martinberlin/H-spi-adapters/1.54-sharp-lcd/schematic/sharp-lcd-back.png

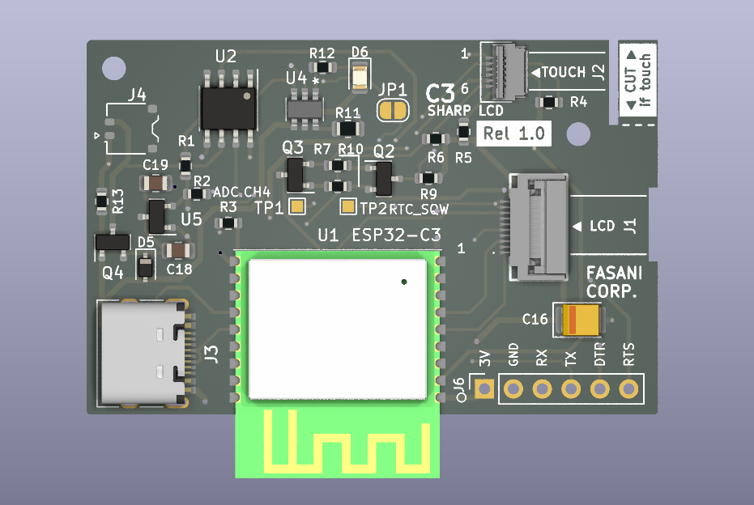
1.54-sharp-lcd/schematic/sharp-lcd-back.png
