martinberlin/H-spi-adapters/1.54-watch-pcb/schematic/EPD_drawing/gooddisplay-GDEY0154D67.jpg

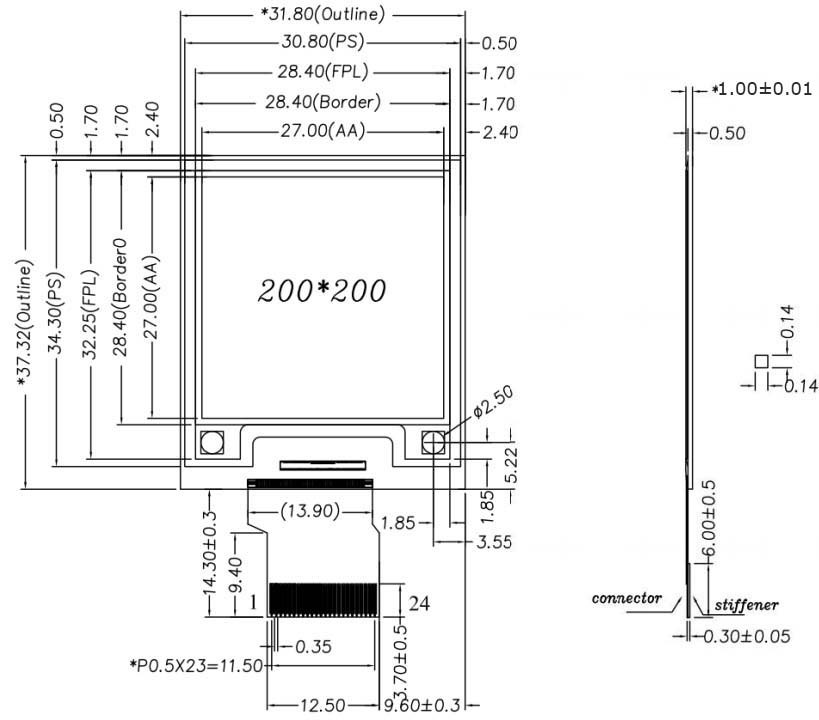
1.54-watch-pcb/schematic/EPD_drawing/gooddisplay-GDEY0154D67.jpg
