martinberlin/H-spi-adapters/tinypico-uc8156/parts/3d/MOSFET_8EDL-T1-GE3_VIS.step

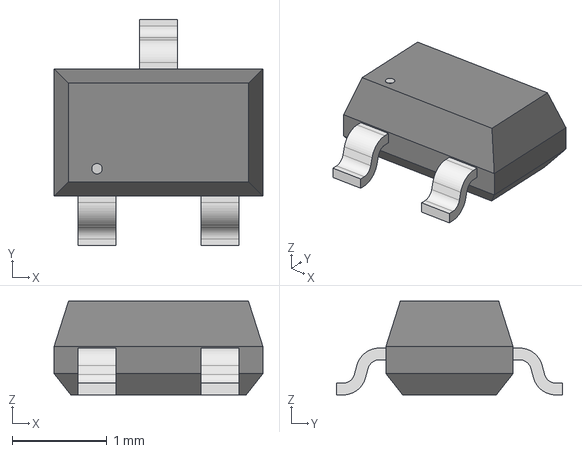
[picture p32: CAD file, 2022-03-19]
tinypico-uc8156/parts/3d/MOSFET_8EDL-T1-GE3_VIS.step
2.21 x 2.39 x 0.993 mm
