martinberlin/H-spi-adapters/sharp-lcd-27/parts/3d/Button_SKRKAH.step

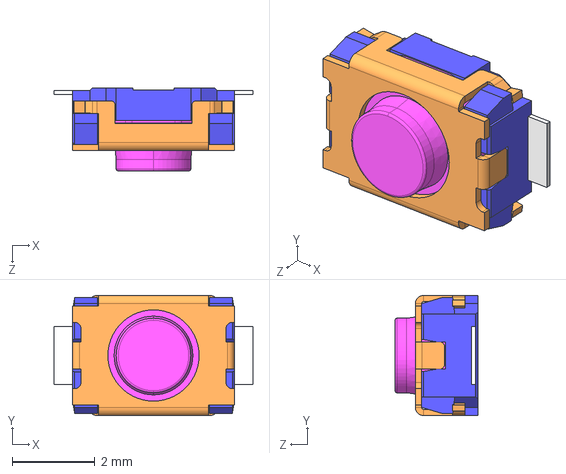
[picture p33: CAD file, 2023-04-13]
sharp-lcd-27/parts/3d/Button_SKRKAH.step
4.80 x 2.90 x 2.00 mm
