martinberlin/H-spi-adapters/C3-27-epaper-touch/parts/3d/0443Series_LTF.step

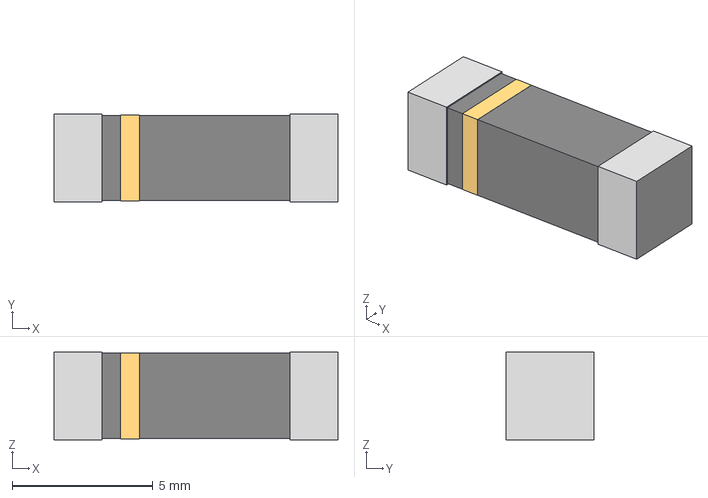
[picture p34: CAD file, 2023-01-21]
C3-27-epaper-touch/parts/3d/0443Series_LTF.step
10.1 x 3.12 x 3.12 mm
