martinberlin/H-spi-adapters/sharp-lcd-27/parts/3d/TP4057-SOT-23.step

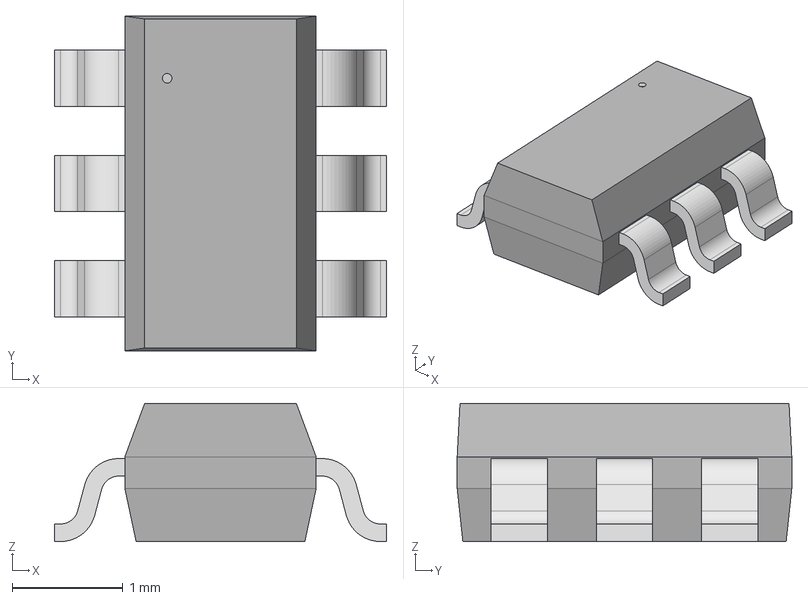
[picture p35: CAD file, 2023-04-13]
sharp-lcd-27/parts/3d/TP4057-SOT-23.step
3.00 x 3.02 x 1.25 mm
