martinberlin/H-spi-adapters/sharp-lcd-27/parts/3d/ESP32-C3-WROOM-02-H4.step

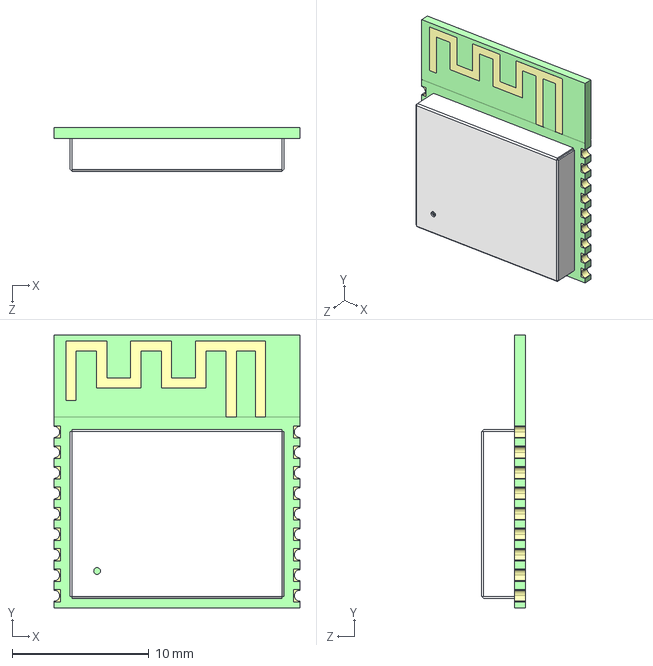
[picture p36: CAD file, 2023-02-09]
sharp-lcd-27/parts/3d/ESP32-C3-WROOM-02-H4.step
18.0 x 20.0 x 3.20 mm
