martinberlin/H-spi-adapters/sharp-lcd-27/parts/3d/FH34SRJ-6S-0.5SH50-Hirose.step

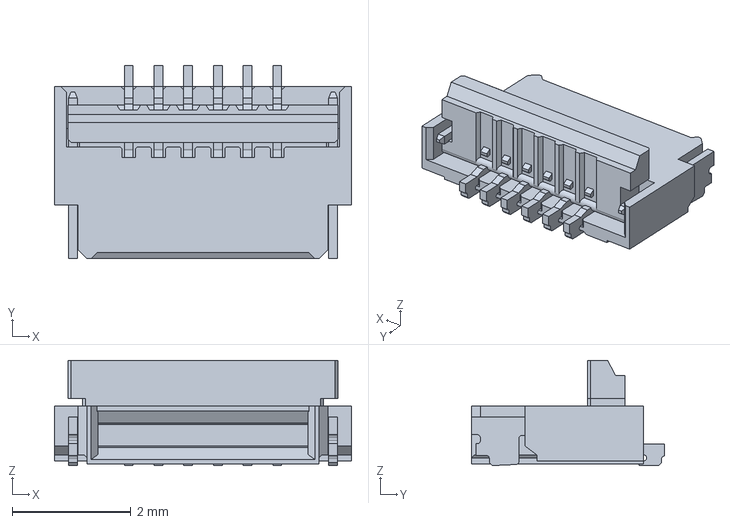
[picture p37: CAD file, 2023-01-21]
sharp-lcd-27/parts/3d/FH34SRJ-6S-0.5SH50-Hirose.step
5.00 x 3.25 x 1.77 mm
