martinberlin/H-spi-adapters/sharp-lcd-27/parts/3d/USB_TYPE-C-31-M-12.step

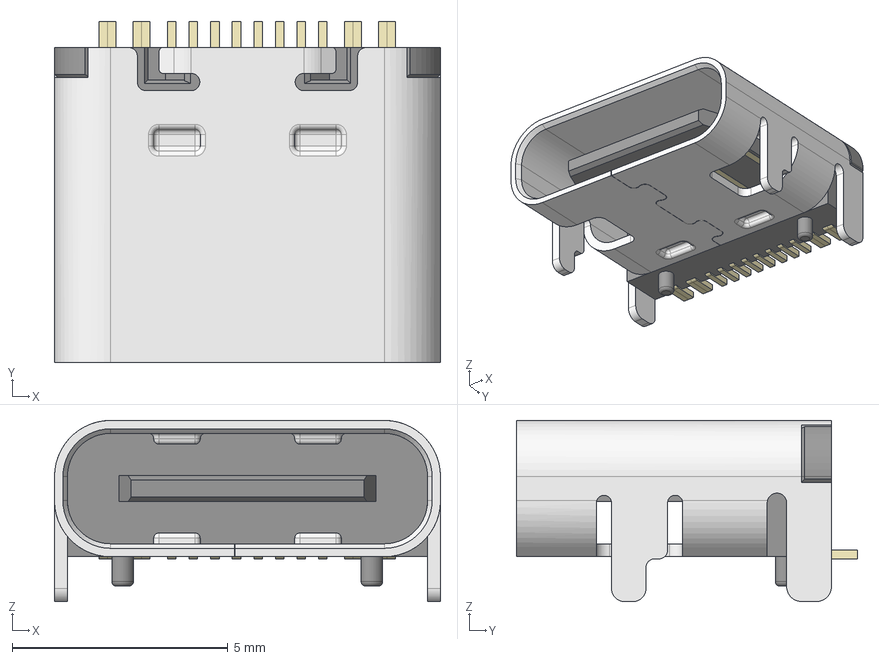
[picture p38: CAD file, 2023-01-21]
sharp-lcd-27/parts/3d/USB_TYPE-C-31-M-12.step
8.95 x 7.90 x 4.20 mm
