martinberlin/H-spi-adapters/sharp-lcd-27/parts/3d/L-40xx.STEP

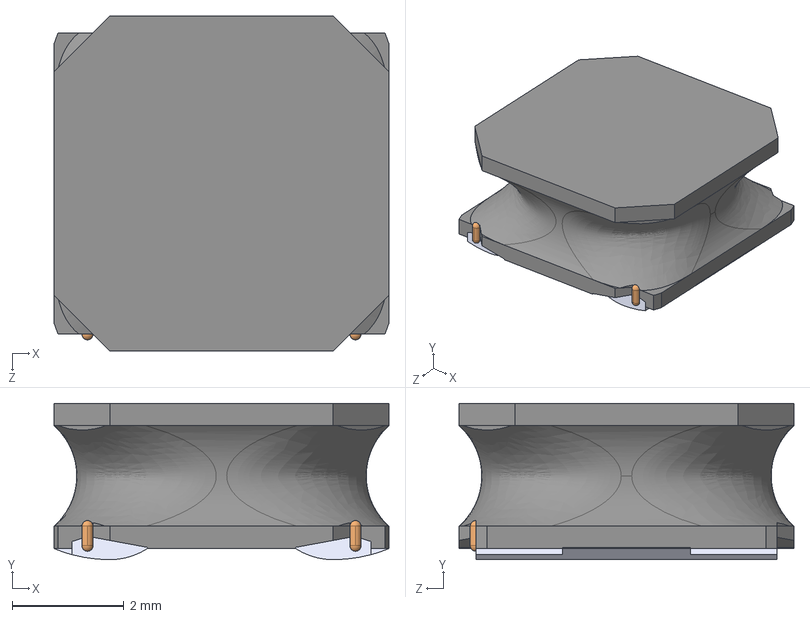
[picture p39: CAD file, 2022-10-17]
sharp-lcd-27/parts/3d/L-40xx.STEP
6.00 x 2.80 x 6.00 mm
