martinberlin/H-spi-adapters/sharp-lcd-27/parts/3d/FH12-24S-0.5SH_55_.step

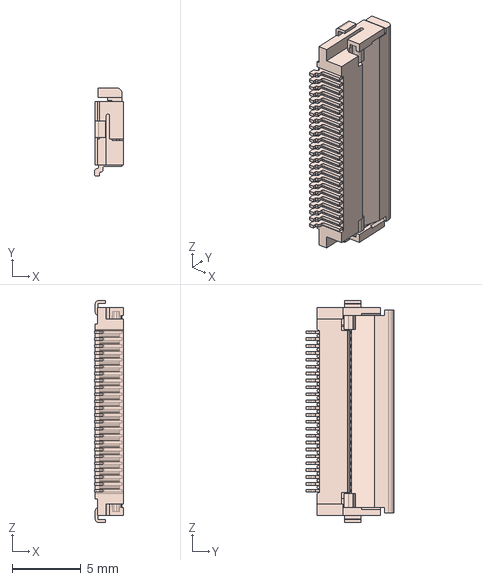
[picture p40: CAD file, 2022-03-20]
sharp-lcd-27/parts/3d/FH12-24S-0.5SH_55_.step
2.10 x 6.40 x 16.1 mm
